pablodz/tesis_pregrado_pucp/Latex/trabajo-de-investigacion-1/images/chapter1/recepcion automatica por bombeo de peces mediante tuberia.pdf

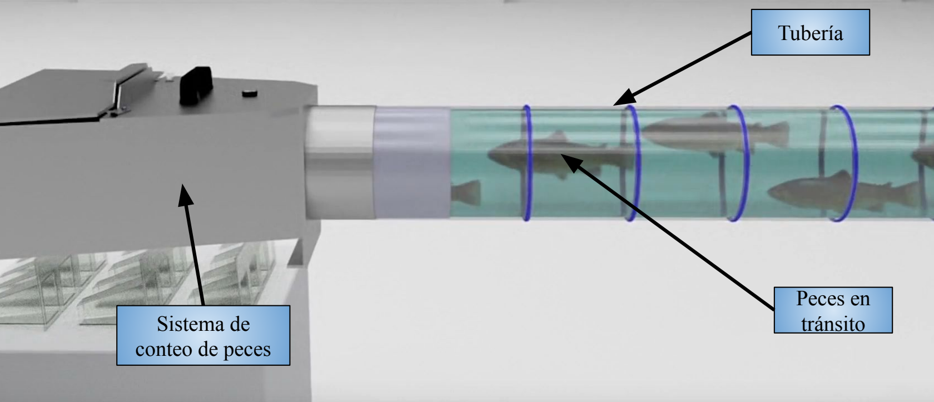
[picture p2: page 1]

Tubería

Peces en
Sistema de | tránsito
conteo de peces
