pablodz/tesis_pregrado_pucp/Latex/trabajo-de-investigacion-2/general/summary.tex

%----------------------------------------------------------------------------------------
%	Resumen
%----------------------------------------------------------------------------------------

\newpage
\clearpage{\pagestyle{empty}\cleardoublepage}
%\doublespacing
\newpage

\pagestyle{empty}
\pagenumbering{roman}
\newpage
\chapter*{\centering \large Resumen} 
\addcontentsline{toc}{chapter}{Resumen} % si queremos que aparezca en el índice
\markboth{Resumen}{Resumen} % encabezado

En el presente trabajo se desarrolla el diseño integral que comprende el diseño de ingeniería basándose en el diseño conceptual realizado en un trabajo previo. Consecuentemente, este trabajo detalla, calcula y evalúa aspectos técnicos del sistema en su conjunto que realiza una clasificación y conteo de truchas en la Laguna de Paucarcocha. La presente propuesta brinda una opción: un sistema semiautomatizado que tiene un precio inferior a las máquinas actualmente comerciables que se adapta a los requerimientos específicos dentro del mercado peruano y simplifica el proceso de clasificación con el fin de disminuir la alta mortandad presente en trabajos manuales. Las simulaciones demuestran un funcionamiento adecuado sistema de detección y conteo de truchas basado en algoritmos de detección de objetos de la arquitectura de redes neuronales YOLO aplicadas a imágenes adquiridas por una cámara estéreo. Finalmente, se concluye que se elaboró un sistema para la clasificación y conteo que sirve para las bases de un prototipo con un costo aproximado de \$4900.

%Considera los siguientes puntos:
%\begin{enumerate}
%	\item Desarrolle un único párrafo (200 a 300 palabras)
%	\item Escriba en tiempo verbal presente
%	\item El resumen debe contener información sobre:
%	\begin{itemize}
%		\item	- La justificación de la investigación
%		\item	- Los objetivos o hipótesis
%		\item	- La teoría o supuestos teóricos o metodológicos en la que se sustenta
%		\item	- El método o procedimiento realizado (de ser necesario)
%		\item	- Los resultados (de ser necesario)
%		\item	- La conclusión principal
%	\end{itemize}
%\end{enumerate}
