pablodz/tesis_pregrado_pucp/Latex/trabajo-de-investigacion-2/general/config.tex

%----------------------------------------------------------------------------------------
%	AUTOR DE LA CONFIGURACIÓN ACTUAL
%----------------------------------------------------------------------------------------

% Pablo Díaz Vergara
% Contáctamen en: pablo.diazv@pucp.edu.pe
% Revisa las últimas actualizaciones en:
% https://bit.ly/2EV6luX
% Versión Cofiguraciones: v2.2
% Fecha: 2020-12-04
% Github: https://github.com/ZurMaD/plantilla_tesis_pucp/

% AVISO: No modificar por su cuenta, enviar un correo para arreglar errores!

%----------------------------------------------------------------------------------------
%	NOMBRE DEL ARCHIVO
%----------------------------------------------------------------------------------------

% Eliminado por bugs en la visualización

%----------------------------------------------------------------------------------------
%	CONFIGURACION DOCUMENTO GENERAL
%----------------------------------------------------------------------------------------

\documentclass[12pt,a4paper,oneside]{thesis} % Formato tesis, 12 tamaño de letra
\setcounter{tocdepth}{4} % Número de indices a indexar en tabla de contenido 2:section 3:subsection 4:subsubsection
\setcounter{secnumdepth}{4} % Número de indices a indexar en tabla de contenido 2:section 3:subsection 4:subsubsection
\usepackage[english]{babel} % Asignar idioma por defecto spanish
%\selectlanguage{spanish} % Idioma por defecto x2
\usepackage[T1]{fontenc} % Aceptar caracteres con tíldes en el pdf generado
\usepackage[UTF8]{ctex}
\usepackage[utf8]{inputenc} % Aceptar caracteres con tíldes en Latex
\usepackage{amsmath} % Para mostrar de forma adecuada las ecuaciones
\usepackage{graphicx} % Para incluir imágenes 
\usepackage{array} % Para incluir imagenes en tablas https://bit.ly/2KXhIlu
\usepackage{float} % Para posicionar imágenes y tablas
\usepackage{multirow} % Fácil manejo de filas
\usepackage{longtable} % Para tablas que abarcan más de dos páginas
\usepackage[table,xcdraw]{xcolor} % Para tablas generadas en https://www.tablesgenerator.com/
% Tamaños de letra dentro de tablas https://texblog.org/2012/08/29/changing-the-font-size-in-latex/
\usepackage{multicol} % Para poder partir en columnas 
\usepackage[refpages]{gloss} % Para enumerar páginas
\usepackage{anysize} % OBSOLETO, NECESITA SER CAMBIADO
\usepackage{bigstrut} % Para automatizar ingresado de datos en tabla
\usepackage{appendix} % Formato para títulos de los apéndices
\usepackage{lscape} % Modifica margenes y rota la página pero no el enumerado
\usepackage{pdflscape} % Cambiar orientación en el pdf
\usepackage{listings} % Sirve para que se compile el Latex
\usepackage{color} % Colores de fondo, texto y otros
\usepackage{setspace} % Espacio entre lineas
\usepackage{enumerate} % Estilo del contador de páginas
\usepackage{ragged2e} % Formato de parrafos, justiticar y demás
\usepackage{comment} % Hacer comentarios en latex
\usepackage{pslatex} % Tipo de fuente
\usepackage{apacite} % Citación en APA
%\usepackage{fixltx2e} % Corrige bugs de Latex 3 | No es necesario en builds >2015
\usepackage{caption} % Objetos flotantes en el documento
\usepackage[top=2.54cm,
bottom=2.54cm,
left=2.54cm,
right=2.54cm,
headheight=17pt, % as per the warning by fancyhdr
includehead,includefoot,
heightrounded, % to avoid spurious underfull messages
]{geometry} % Márgenes para contenido y líneas de pie y cabecera de página
\usepackage{fancyhdr} % Cabeza y pie de página 
\usepackage{blindtext}
\usepackage{pdfpages} % Cargar imagenes en pdf
\usepackage{datetime} % Fecha

\usepackage{footnote} % Tablas largas y foot note para tablas https://texblog.org/2012/02/03/using-footnote-in-a-table/
\usepackage{enumitem} % Enumerar letras
\usepackage[bottom]{footmisc} % Forzar notas de página pegadas hacia abajo https://bit.ly/3fyOA2f
\usepackage{scrextend} % Cambiar formato nota de página
\deffootnote[.5in]{.5in}{.195in}{\makebox[.5in][r]{\thefootnotemark.\hspace{.2in}}}  % Cambiar formato nota de página
% ERROR DE "TITLE ALREADY DEFINED" Pueden omitirlo, no afecta en nada, pueden comentarlo incluso en el archivo.sty

\usepackage[paper=portrait,pagesize]{typearea} %PORTRAID-LANDSCAPE 

\usepackage{url} % Evitar enlaces en bibliografía largos & enlazar enlaces de bibliografía
\usepackage{breakurl} % Broken links
\usepackage[hyperfootnotes=false]{hyperref} % Evitar enlaces en bibliografía largos & enlazar enlaces de bibliografía ADEMAS, false porque así lo recomienda la libreria footmisc
\usepackage{natbib}
\usepackage{etoolbox}

\usepackage{mathptmx} % Times News Roman
\usepackage{titlesec} % Cambiar chapter style
\usepackage{indentfirst} % Agregar indentado de 1cm al inicio de cada párrafo de cada sección

%\usepackage{svg} % Soporte imagenes svg
% SVG necesita agregar --shel por eso no lo usaremos

%----------------------------------------------------------------------------------------
%	CONFIGURACION ESPACIADO, TAMAÑO DE LETRA Y RELACIONADOS A FIGURAS, TABLAS
%----------------------------------------------------------------------------------------
% Documentación \captionsetup https://bit.ly/31RjwG3 

% FIGURAS
\captionsetup[figure]{font={footnotesize,singlespacing}} % https://bit.ly/2QOHo6U
\captionsetup[figure]{labelfont={bf}} % Negrita a Tabla X.X
\captionsetup[figure]{labelsep={endash}} % Punto y espacio luego de Figura X.X. 
\captionsetup[figure]{width={.75\textwidth}} % Sangría para título de Figura
\captionsetup[figure]{justification=centerlast} % Justificado, última linea centrado
\captionsetup[figure]{aboveskip=7pt} % https://bit.ly/3jIe7HF Foro latex
\captionsetup[figure]{belowskip=7pt} 
\captionsetup[figure]{skip=0pt} % Posición figuras
\captionsetup[figure]{position=below} % Posición figuras
\captionsetup[figure]{name=Figura} % Nombre figuras

% TABLAS
\captionsetup[table]{font={footnotesize,singlespacing}} % scriptsize,footnotesize,small,normalsize,larga,Large %stretch=0.8
\captionsetup[table]{labelfont={bf}} % normalfont,up,it,sl,sc,md,bf,rm,sf,tt
\captionsetup[table]{labelsep={endash}} % none,colon,period,space,quad,newline,endash 
\captionsetup[table]{width={.75\textwidth}} % Sangría para título de tabla
\captionsetup[table]{justification=centerlast} % Justificado, última linea centrado
\captionsetup[table]{aboveskip=7pt} % Espaciado arriba del título
\captionsetup[table]{belowskip=7pt} % Espaciado abajo del título
\captionsetup[table]{skip=0pt} % Posición tablas
\captionsetup[table]{position=above} % Posición tablas
\captionsetup[table]{name=Tabla} % Nombre figuras

%----------------------------------------------------------------------------------------
%	CONFIGURACION SECCIONES DE CÓDIGO
%----------------------------------------------------------------------------------------

% Eliminado, contenia bugs, la siguiente versión se implementa

%----------------------------------------------------------------------------------------
%	CONFIGURACION FORMATO SECCIONES
%----------------------------------------------------------------------------------------

%%%%%%%%%%%%%%%%%%%%%%%%%%%%%%%%%%%%%%%%%%%%%%%%%%%%%%
% PÁGINA DE CAPÍTULOS ES AUTOMÁTICO TIPO PLAIN       %
%%%%%%%%%%%%%%%%%%%%%%%%%%%%%%%%%%%%%%%%%%%%%%%%%%%%%%
\fancypagestyle{plain}{
	\fancyhead{}% clear all header 
	\fancyfoot{}% clear all footer
	\fancyhf{}% clear all header and footer fields	
	\fancyhead[L,C,R]{}
	\fancyfoot[L,C,R]{}
	\fancyfoot[C]{Página \thepage}
	\renewcommand{\headrulewidth}{0.4pt}
	\renewcommand{\footrulewidth}{0.4pt}
	\newgeometry{
		top=2.54cm,
		bottom=2.54cm,
		left=2.54cm,
		right=2.54cm,
		headheight=17pt, % as per the warning by fancyhdr
		includehead,includefoot,
		heightrounded % to avoid spurious underfull messages
	}
}
%%%%%%%%%%%%%%%%%%%%%%%%%%%%%%%%%%%%%%%%%%%%%%%%%%%%%%
% PÁGINA VERTICAL                                    %
%%%%%%%%%%%%%%%%%%%%%%%%%%%%%%%%%%%%%%%%%%%%%%%%%%%%%%
\fancypagestyle{myportland}{
	\fancyhead{}% clear all header 
	\fancyfoot{}% clear all footer
	\fancyhf{}% clear all header and footer fields	
	\fancyhead[L,C,R]{}
	\fancyfoot[L,C,R]{}
	\fancyfoot[C]{Página \thepage}
	\renewcommand{\headrulewidth}{0.4pt}
	\renewcommand{\footrulewidth}{0.4pt}
	\newgeometry{
		top=2.54cm,
		bottom=2.54cm,
		left=2.54cm,
		right=2.54cm,
		headheight=17pt, % as per the warning by fancyhdr
		includehead,includefoot,
		heightrounded % to avoid spurious underfull messages
	}
}
%%%%%%%%%%%%%%%%%%%%%%%%%%%%%%%%%%%%%%%%%%%%%%%%%%%%%%
% PÁGINA HORIZONTAL                                  %
%%%%%%%%%%%%%%%%%%%%%%%%%%%%%%%%%%%%%%%%%%%%%%%%%%%%%%
% https://tex.stackexchange.com/questions/337/how-to-change-certain-pages-into-landscape-portrait-mode
\fancypagestyle{mylandscape}{
	\fancyhead{}% clear all header 
	\fancyfoot{}% clear all footer
	\fancyhf{}% clear all header and footer fields	
	\fancyhead[LO,RE]{}
	\fancyfoot[LO,RE]{}
	\fancyfoot{% Footer
		\makebox[\textwidth][r]{% Right
			\rlap{\hspace{0.75cm}% Push out of margin by \footskip
				\smash{% Remove vertical height
					\raisebox{4.87in}{% Raise vertically
						\rotatebox{90}{Página \thepage}}}}}}% Rotate counter-clockwise
	\renewcommand{\headrulewidth}{0pt}% No header rule
	\renewcommand{\footrulewidth}{0pt}% No footer rule
	\newgeometry{
		top=3.54cm, % Now top is → right
		bottom=2.54cm, % Now botton is ← left
		left=2.40cm, % Now left is ↑ top
		right=2cm, % Now right is ↓ bottom
	}
}

%----------------------------------------------------------------------------------------
%	UTILIDADES
%----------------------------------------------------------------------------------------

\newcommand*\rot{\rotatebox{90}} % Poder rotar 90° texto, imagenes, lo que sea
\graphicspath{{images/}} % Directorio que contiene imagenes

%----------------------------------------------------------------------------------------
%	CONFIGURACION NOMBRE DE TÍTULOS, CAPÍTULOS, TABLAS, ÍNDICES
%----------------------------------------------------------------------------------------

%%%%%%%%%%%%%%%%%%%%%%%%%%%%%%%%%%%%%%%%%%%%%%%%%%%%%%
% CAMBIO DE FORMATO DE CAPÍTULOS                     %
%%%%%%%%%%%%%%%%%%%%%%%%%%%%%%%%%%%%%%%%%%%%%%%%%%%%%%

% CHAPTER X
\titleformat{\chapter}
{\large\bfseries\filcenter}{\thechapter}{1em}{}
% SECTION X.X
\titleformat{\section}
{\normalfont\bfseries\filright}{\thesection}{1em}{}

% SUBSECTION X.X.X
\titleformat{\subsection}
{\normalfont\bfseries\filright}{\thesubsection}{1em}{}

% SUBSUBSECTION X.X.X.X
\titleformat{\subsubsection}
{\normalfont\bfseries\filright}{\thesubsubsection}{1em}{}

% Dentro del siguiente código no usar comentarios
% ENUMERACIÓN arabic Arabic Roman roman
\addto\captionsenglish{
	\renewcommand{\contentsname}{Índice}
	\renewcommand{\listfigurename}{Índice de figuras}
	\renewcommand{\listtablename}{Índice de tablas}
	\renewcommand{\baselinestretch}{2}
	\renewcommand{\appendixname}{Anexos}
	\renewcommand{\appendixtocname}{Anexos}
	\renewcommand{\appendixpagename}{Anexos}
	\renewcommand{\chaptername}{Capítulo}
	\renewcommand{\thetable}{Tabla}	
	\renewcommand{\thefigure}{Figura}
	\renewcommand{\thechapter}{Capítulo \arabic{chapter}}
	\renewcommand{\thesection}{\arabic{chapter}.\arabic{section}}
	\renewcommand{\thetable}{\arabic{chapter}.\arabic{table}}
	\renewcommand{\thefigure}{\arabic{chapter}.\arabic{figure}}
	\renewcommand{\theequation}{\arabic{chapter}.\arabic{equation}}
}

\renewcommand{\bibsection}{} % Eliminar "References" como título de lista de bibliografía

%%%%%%%%%%%%%%%%%%%%%%%%%%%%%%%%%%%%%%%%%%%%%%%%%%%%%%
% MODO 1: ENUMERACIÓN POR CAPÍTULOS 1.1,1.2,2.1,...  %
%%%%%%%%%%%%%%%%%%%%%%%%%%%%%%%%%%%%%%%%%%%%%%%%%%%%%%
%\renewcommand{\thetable}{\arabic{chapter}.\arabic{table}}
%\renewcommand{\thefigure}{\arabic{chapter}.\arabic{figure}}
%\renewcommand{\theequation}{\arabic{chapter}.\arabic{equation}}
%%%%%%%%%%%%%%%%%%%%%%%%%%%%%%%%%%%%%%%%%%%%%%%%%%%%%%
% MODO 2: ENUMERACIÓN ARÁBICA SECUENCIAL 1,2,3,4,... %
%%%%%%%%%%%%%%%%%%%%%%%%%%%%%%%%%%%%%%%%%%%%%%%%%%%%%%
%\renewcommand{\thetable}{\arabic{1}}
%\renewcommand{\thefigure}{\arabic{1}}
%\renewcommand{\theequation}{\arabic{1}}

%----------------------------------------------------------------------------------------
%	CONSTANTES GLOBALES
%----------------------------------------------------------------------------------------

\newcommand{\myarraystrech}{0.75}

\newcommand{\mymaxsizeofcontenttable}{3 cm}
\newcommand{\mysizeimageinsidetable}{1.5 cm}

\newcommand{\mysecondmaxsizeofcontenttable}{5 cm}
\newcommand{\mysecondmaxsizeimageinsidetable}{4 cm}

\newcommand{\mythirdmaxsizeofcontenttable}{2.6 cm}
\newcommand{\mythirdmaxsizeimageinsidetable}{2.4 cm}

\newcommand{\myforthmaxsizeofcontenttable}{4 cm}

\newenvironment{myflushcenter}{%
	\vspace{-1.5em}
	\begin{center}
	}{%
	\end{center}
}

\newenvironment{myflushcenterinsidetable}{%
	\setstretch{0.75}
	\setlength\topsep{0pt}
	\setlength\parskip{0pt}
	\begin{center}
	}{%
	\end{center}
}

\newenvironment{myflushleftinsidetable}{%
	\setstretch{0.75}
	\setlength\topsep{0pt}
	\setlength\parskip{0pt}
	\begin{flushleft}
	}{%
	\end{flushleft}
}

\newenvironment{myflushcenteraftertable}{%
	\vspace{-0.5 em}
	\begin{center}
	}{%
	\end{center}
}

% Para datos debajo de imagenes en páginas verticales
\newenvironment{myflushleftportland}{%
	\vspace{-1.5em}
	\begin{flushleft} 
	\footnotesize
	}{%
	\end{flushleft}
}

% Para datos debajo de tablas en páginas verticales
\newenvironment{myflushleftportland2}{%
	\vspace{-2.5em}
	\begin{flushleft} 
	\footnotesize
	}{%
	\end{flushleft}
}

% Para datos debajo de tablas e imagenes en páginas verticales
\newenvironment{myflushleftlandscape}{%
	\vspace{-3em}
	\begin{flushleft} 
	\footnotesize
	}{%
	\end{flushleft}
}

% Para evitar espacios luego de nombre de imagen
\newenvironment{myfigure}{%
	\vspace{-0.10em}
	\begin{figure}
	}{%
	\end{figure}
	\vspace{-1.5em}
}

% Para evitar espacios luego de la tabla
\newenvironment{mytable}{%
	\vspace{-1.0em}
	\begin{table}
	}{%
	\end{table}
	\vspace{-1.5em}
}

% Para evitar espacios en ecuaciones
\newenvironment{myequation}{%
	\vspace{-2.5em}
	\begin{equation}
	}{%
	\end{equation}
	\vspace{-2.0em}
}

%----------------------------------------------------------------------------------------
%	CONFIGURACION BIBLIOGRAFIA
%----------------------------------------------------------------------------------------

\bibliographystyle{apacite}
\renewcommand{\BOthers}[1]{et al.\hbox{}}%       et al
\renewcommand{\BOthersPeriod}[1]{et al.\hbox{}}%  et al.
% CONTINUA EN BIBLIOGRAPHY.TEX

%----------------------------------------------------------------------------------------
%	CONFIGURACION DE MARGENES EN TABLA DE CONTENIDOS, COMENTAR SI QUIERES QUE SALGA CON INDENTADOS
%----------------------------------------------------------------------------------------

% Será actualizado en la siguiente versión...

%----------------------------------------------------------------------------------------
%	CONFIGURACION NOTAS DE PAGINA
%----------------------------------------------------------------------------------------

\setlength{\footskip}{25pt} % Elimina espacios luego de notas de pagina
