pablodz/tesis_pregrado_pucp/Latex/trabajo-de-investigacion-1/general/conclusions.tex

%----------------------------------------------------------------------------------------
%	Agradecimientos
%----------------------------------------------------------------------------------------

\pagestyle{myportland}
\doublespacing
%\pagenumbering{arabic}
\chapter*{\centering \large Conclusiones}
\addcontentsline{toc}{chapter}{Conclusiones}
\markboth{Conclusiones}{Conclusiones}
\thispagestyle{myportland}

Se detectaron procesos críticos en la crianza de truchas y se seleccionó el proceso manual que disminuía la producción final generando pérdidas económicas: clasificación y conteo de truchas en la etapa de engorde (15 a 20 centímetros).

Se elaboró la lista de requerimientos según una entrevista con personas dedicadas al cultivo de truchas. Se propuso tres conceptos de solución y se escogió uno de estos bajo un análisis técnico-económico. El concepto de solución óptimo cumple con todos los puntos de la lista de requerimientos. Además, se realizó el diagrama de operaciones necesario para mostrar el funcionamiento de la máquina.

Para el análisis de estabilidad y flotabilidad sobre el agua del concepto de solución óptimo será necesario realizar cálculos y mediciones.

Una estimación simple sin detalle del concepto de solución óptimo muestra un costo menor comparado con el costo de una máquina que se comercializa internacional-mente. Además, el costo de operación disminuye debido a que se reduce el número de operarios de cuatro a solo uno.

El trabajo presentado permite la extrapolación de dimensiones de las tuberías para poder emplear diferentes tallas de truchas. Es decir, una máquina de clasificación y conteo fuera del rango propuesto de 10 a 20 cm.
