pablodz/tesis_pregrado_pucp/Latex/trabajo-de-investigacion-1/images/chapter3/concepto virtual del concepto de solucion 2.pdf

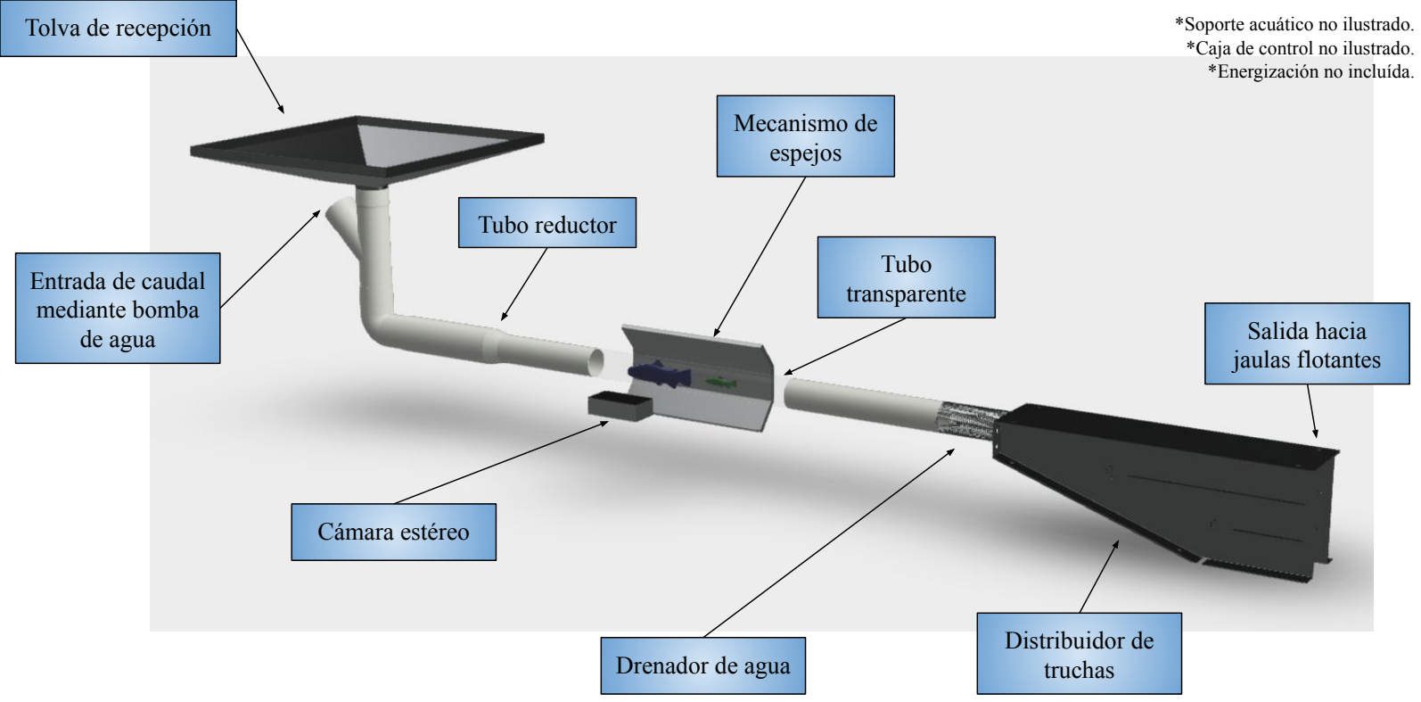
[picture p191: page 1]

Tolva de recepción

Entrada de caudal
mediante bomba
de agua

Cámara estéreo

Drenador de agua

Distribuidor de
truchas

Salida hacia
jaulas flotantes

Tubo reductor

Tubo
transparente

Mecanismo de
espejos

*Soporte acuático no ilustrado. *Caja de control no ilustrado. *Energización no incluída.
