pablodz/tesis_pregrado_pucp/Latex/trabajo-de-investigacion-1/images/chapter1/maquina seleccionadora de truchas agv.pdf

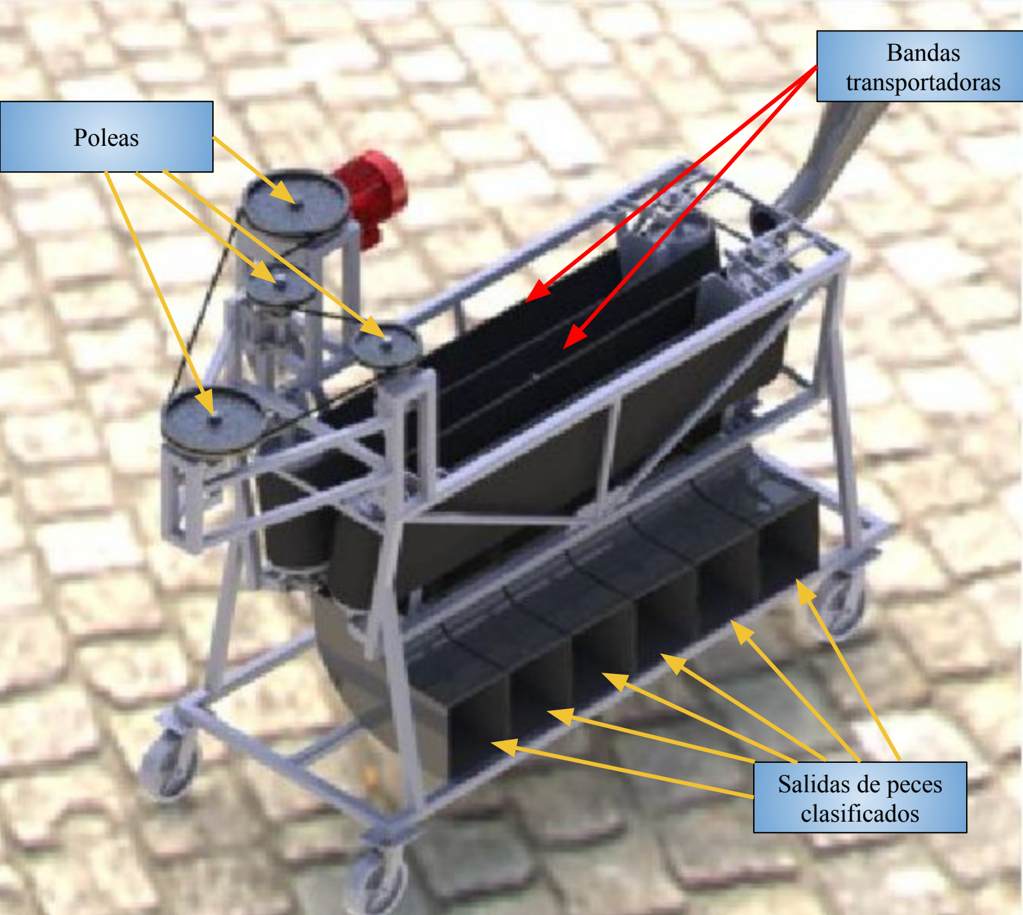
[picture p192: page 1]

Bandas
transportadoras

Salidas de peces
clasificados

Poleas
