pablodz/tesis_pregrado_pucp/Latex/trabajo-de-investigacion-1/images/chapter1/contador pescavision 100 300 10x4.pdf

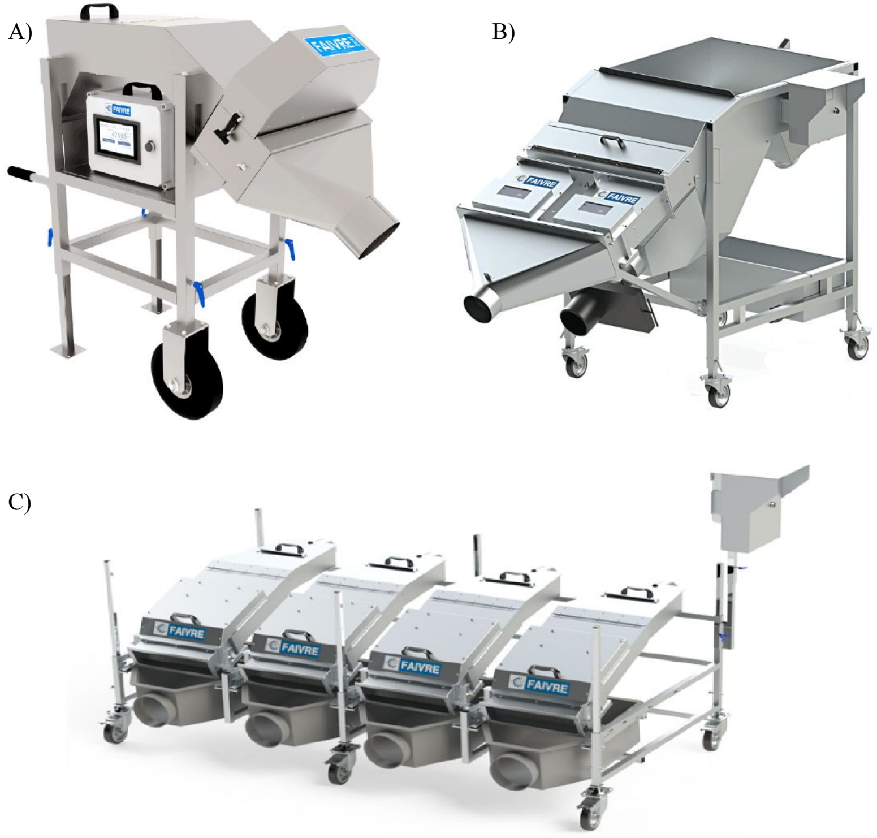
[picture p193: page 1]

A) B)

C)
