pablodz/tesis_pregrado_pucp/Latex/trabajo-de-investigacion-1/images/chapter1/clasificacion conteo curado y calculo de biomasa en la laguna de canrash.pdf

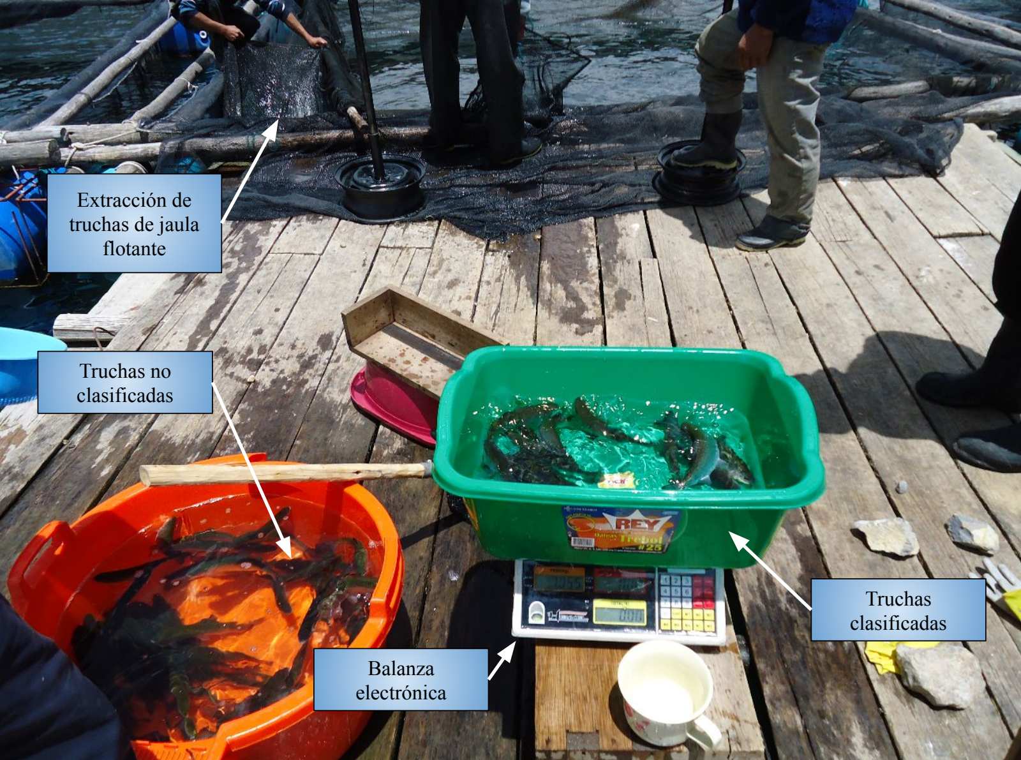
[picture p194: page 1]

Extracción de
truchas de jaula
flotante

Truchas no
clasificadas

Balanza
electrónica

Truchas
clasificadas
