pablodz/tesis_pregrado_pucp/Latex/trabajo-de-investigacion-1/images/chapter1/extraccion de caracteristicas mediante vision por computadora.pdf

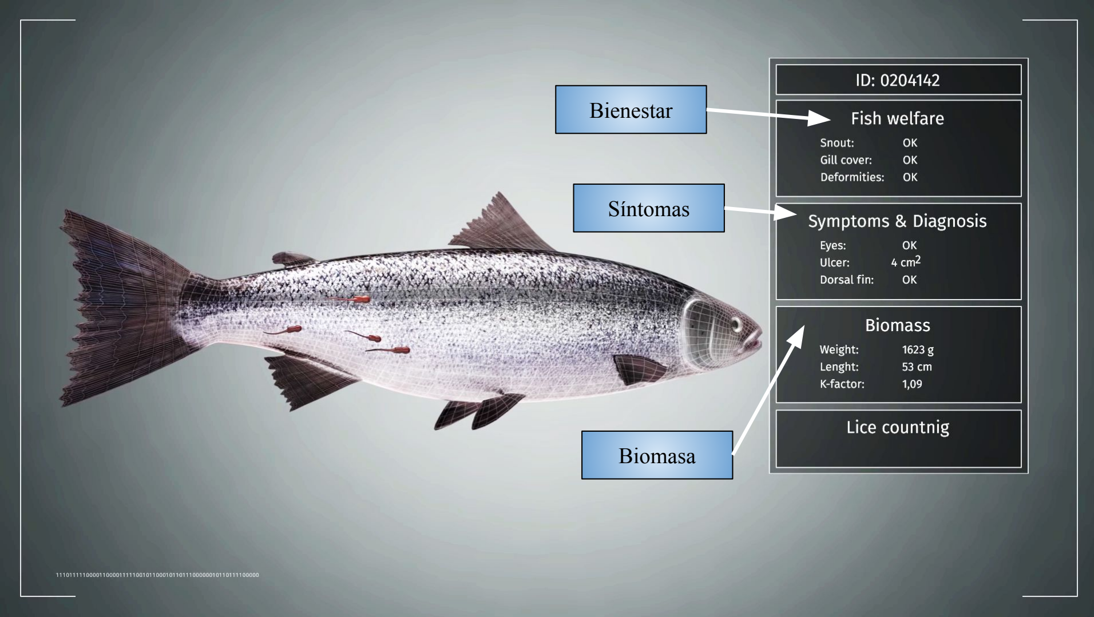
[picture p195: page 1]

Bienestar

Síntomas

Biomasa
