pablodz/tesis_pregrado_pucp/Latex/trabajo-de-investigacion-1/images/chapter1/planos comunes de posicionamiento para camaras de inspeccion.pdf

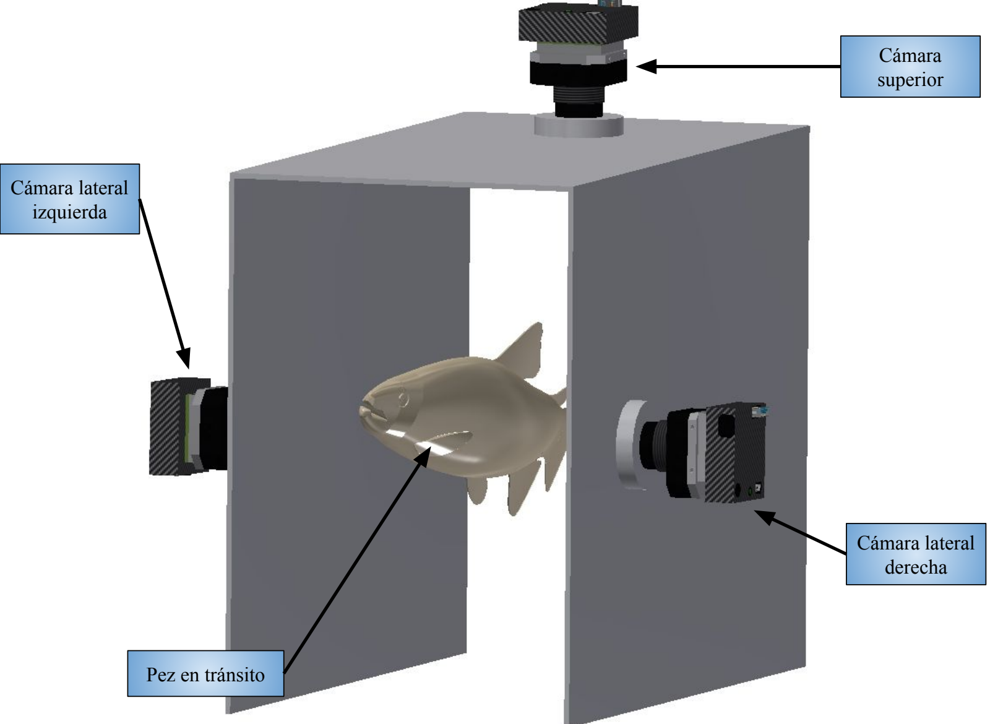
[picture p196: page 1]

Cámara lateral
izquierda

Pez en tránsito

Cámara
superior

Cámara lateral
derecha
