pablodz/tesis_pregrado_pucp/Latex/trabajo-de-investigacion-1/images/chapter1/usando relacion entre a y b para calcular longitud del pez.pdf

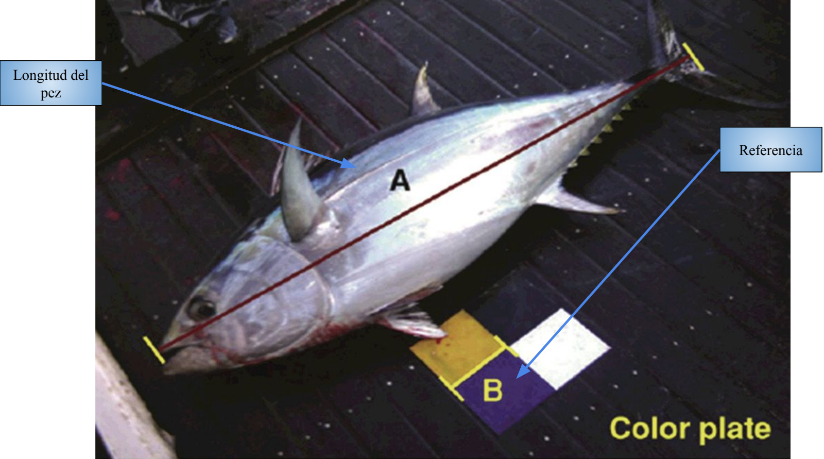
[picture p197: page 1]

Referencia

Longitud del
pez
