pablodz/tesis_pregrado_pucp/Latex/trabajo-de-investigacion-1/images/chapter1/extraccion trucha toneladas anuales.png

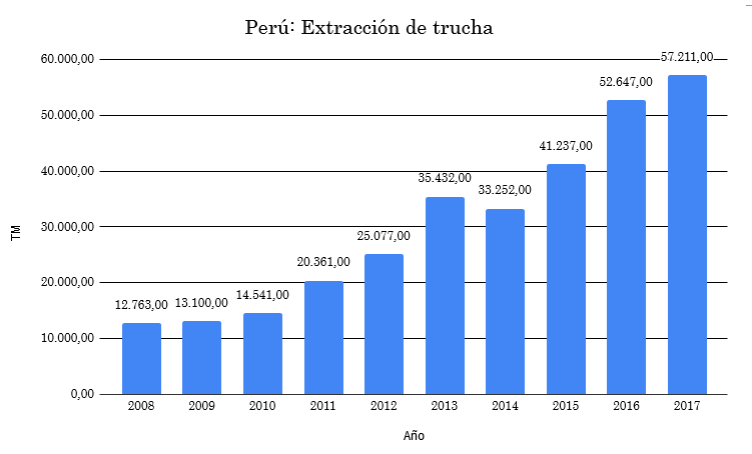
Latex/trabajo-de-investigacion-1/images/chapter1/extraccion trucha toneladas anuales.png
