pablodz/tesis_pregrado_pucp/Latex/trabajo-de-investigacion-1/images/chapter1/medicion de peces dentro de estanques con camaras ortogonales.png

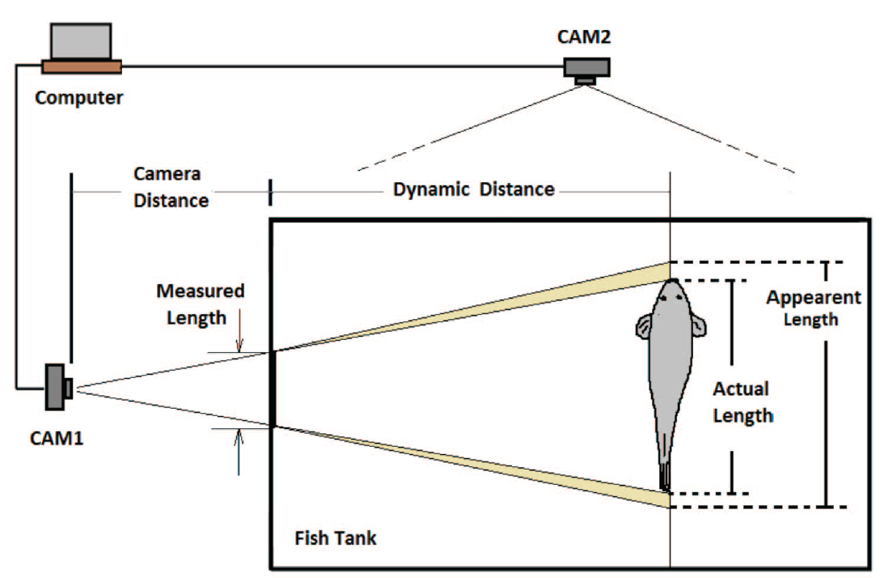
Latex/trabajo-de-investigacion-1/images/chapter1/medicion de peces dentro de estanques con camaras ortogonales.png
