pablodz/tesis_pregrado_pucp/Latex/trabajo-de-investigacion-1/images/chapter1/pez identificado por una red neuronal.png

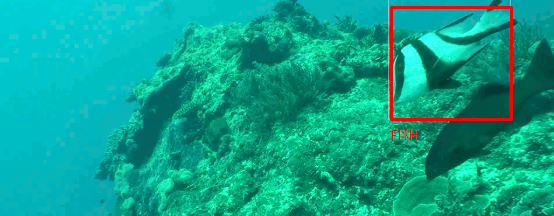
Latex/trabajo-de-investigacion-1/images/chapter1/pez identificado por una red neuronal.png
