pablodz/tesis_pregrado_pucp/Latex/trabajo-de-investigacion-1/images/chapter3/matriz/fuente de alimentacion.png

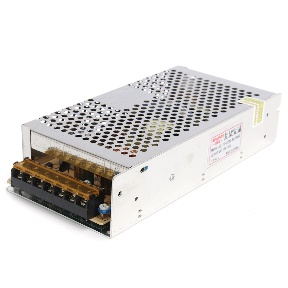
Latex/trabajo-de-investigacion-1/images/chapter3/matriz/fuente de alimentacion.png
