pablodz/tesis_pregrado_pucp/Latex/trabajo-de-investigacion-1/images/chapter3/matriz/tarjeta electronica para control de actuadores lineales.png

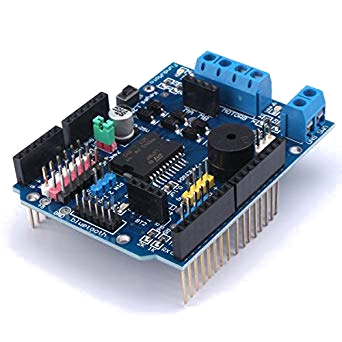
Latex/trabajo-de-investigacion-1/images/chapter3/matriz/tarjeta electronica para control de actuadores lineales.png
