pablodz/tesis_pregrado_pucp/Latex/trabajo-de-investigacion-1/images/chapter3/matriz/variador de voltaje.png

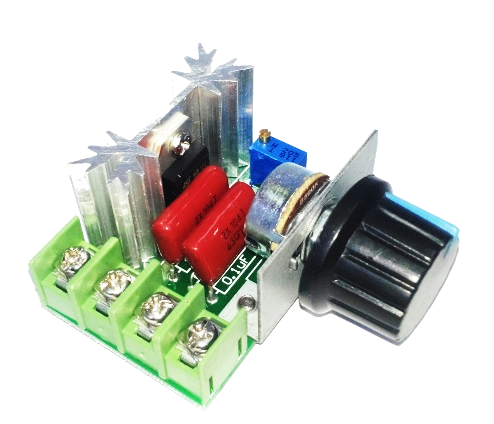
Latex/trabajo-de-investigacion-1/images/chapter3/matriz/variador de voltaje.png
