pablodz/tesis_pregrado_pucp/Latex/trabajo-de-investigacion-1/images/introduction/produccion agricola mundial.png

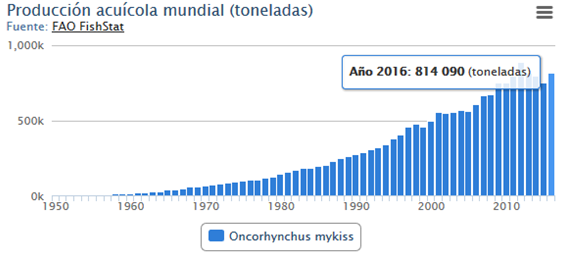
Latex/trabajo-de-investigacion-1/images/introduction/produccion agricola mundial.png
