pablodz/tesis_pregrado_pucp/Latex/trabajo-de-investigacion-2/images/chapter1/medicion de peces dentro de estanques con camaras estereo.png

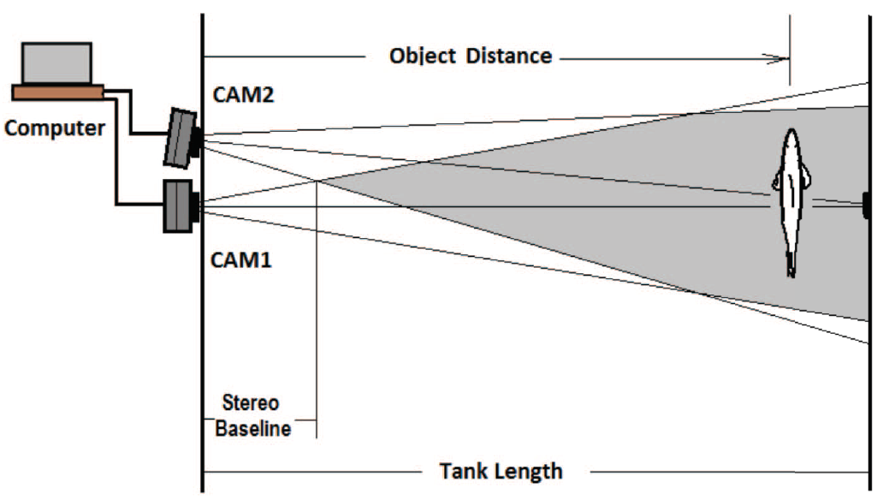
Latex/trabajo-de-investigacion-2/images/chapter1/medicion de peces dentro de estanques con camaras estereo.png
