pablodz/tesis_pregrado_pucp/Latex/trabajo-de-investigacion-2/images/chapter3/matriz/boton de emergencia.png

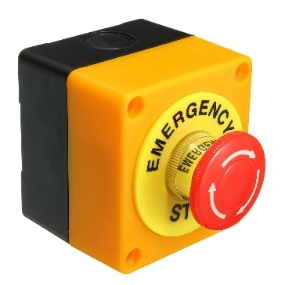
Latex/trabajo-de-investigacion-2/images/chapter3/matriz/boton de emergencia.png
