pablodz/tesis_pregrado_pucp/Latex/trabajo-de-investigacion-2/images/chapter5/aplicacion movil login.png

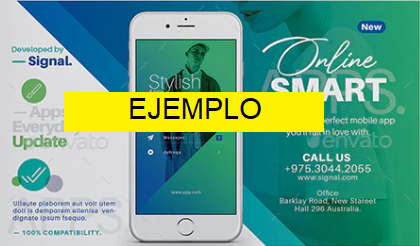
Latex/trabajo-de-investigacion-2/images/chapter5/aplicacion movil login.png
