pablodz/tesis_pregrado_pucp/Latex/trabajo-de-investigacion-2/images/chapter5/concepto optimo tuberias.png

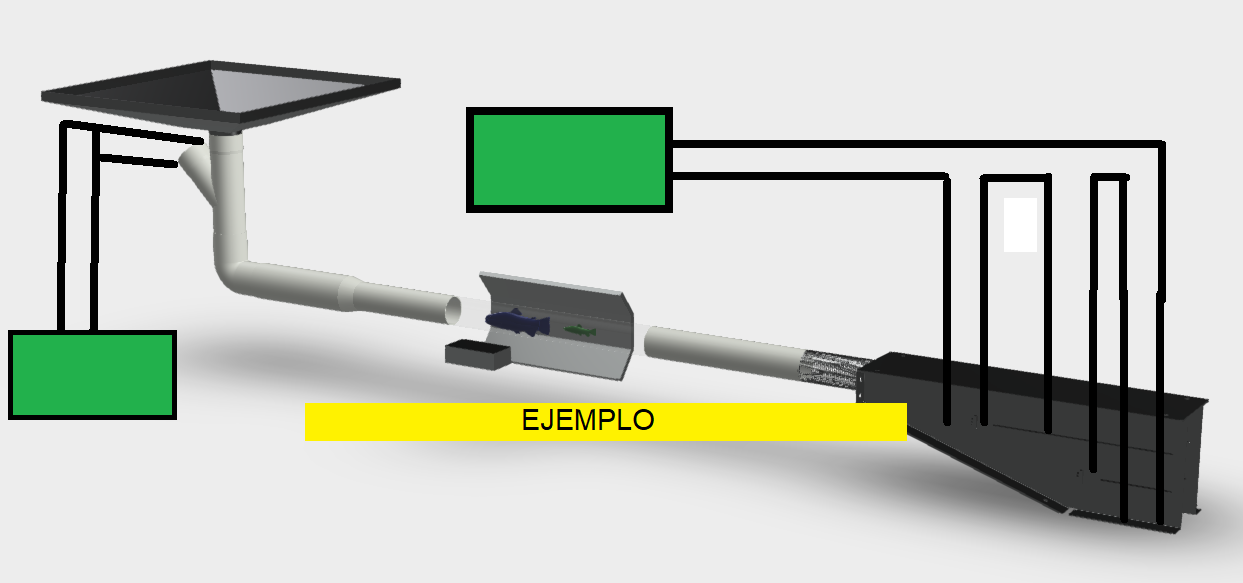
Latex/trabajo-de-investigacion-2/images/chapter5/concepto optimo tuberias.png
