pablodz/tesis_pregrado_pucp/Latex/trabajo-de-investigacion-2/images/chapter5/control electrovalvulas pid.png

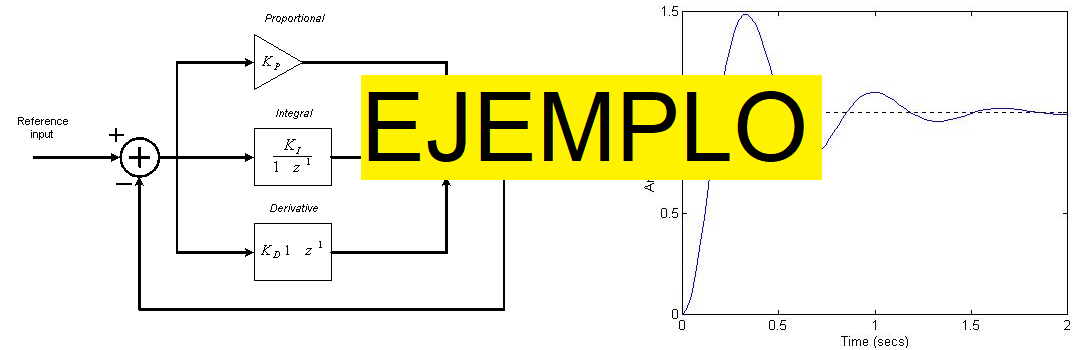
Latex/trabajo-de-investigacion-2/images/chapter5/control electrovalvulas pid.png
