pablodz/tesis_pregrado_pucp/Latex/trabajo-de-investigacion-2/images/chapter5/distancia entre espejos y camara ejemplo.png

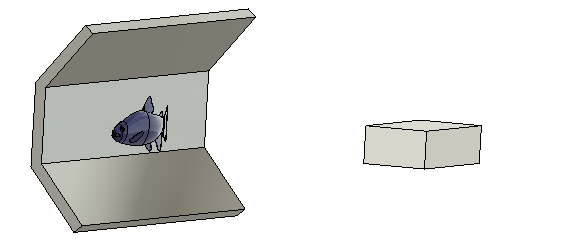
Latex/trabajo-de-investigacion-2/images/chapter5/distancia entre espejos y camara ejemplo.png
