pablodz/tesis_pregrado_pucp/Latex/trabajo-de-investigacion-2/images/chapter5/ejemplo de tabla.png

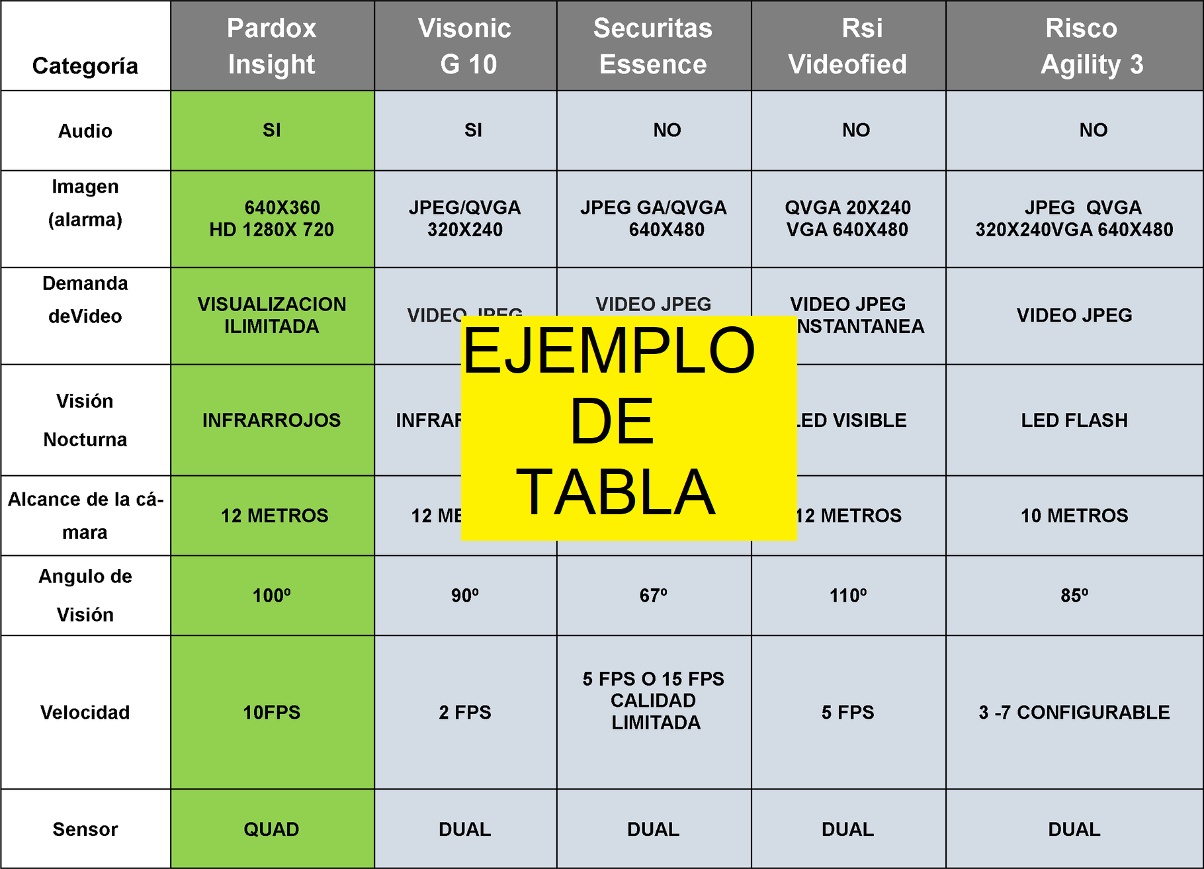
Latex/trabajo-de-investigacion-2/images/chapter5/ejemplo de tabla.png
