pablodz/tesis_pregrado_pucp/Latex/trabajo-de-investigacion-2/images/chapter5/frontend/frames (6).png

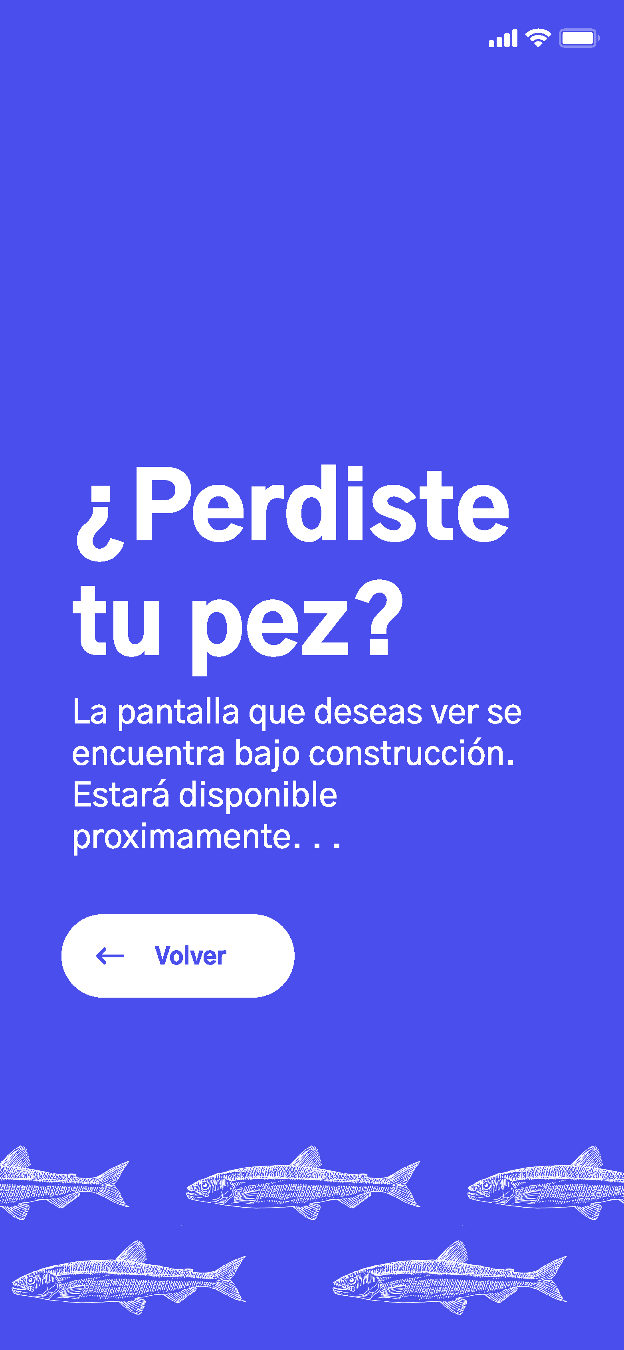
Latex/trabajo-de-investigacion-2/images/chapter5/frontend/frames (6).png
