pablodz/tesis_pregrado_pucp/Latex/trabajo-de-investigacion-2/images/chapter5/frontend/frames (9).png

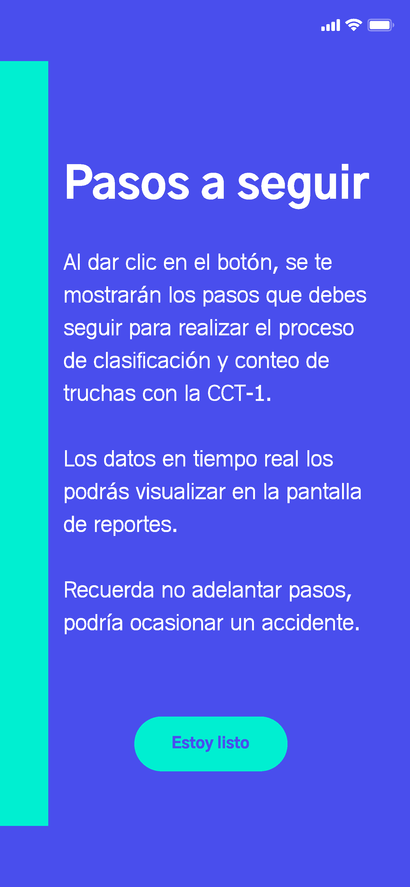
Latex/trabajo-de-investigacion-2/images/chapter5/frontend/frames (9).png
