pablodz/tesis_pregrado_pucp/Latex/trabajo-de-investigacion-2/images/chapter5/iluminacion 2 tiras led.png

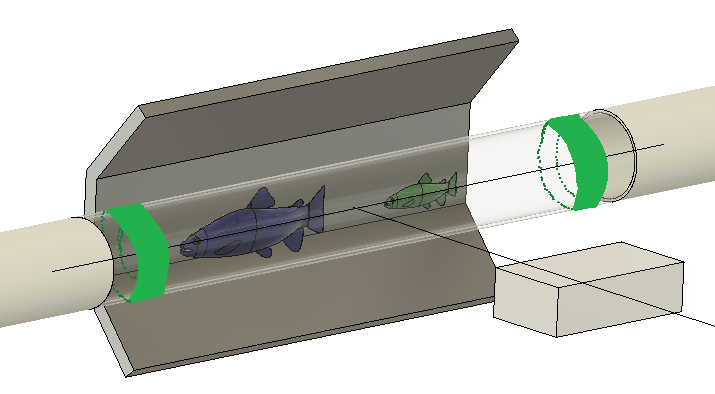
Latex/trabajo-de-investigacion-2/images/chapter5/iluminacion 2 tiras led.png
