pablodz/tesis_pregrado_pucp/Latex/trabajo-de-investigacion-2/images/chapter5/iluminacion 4 leds.png

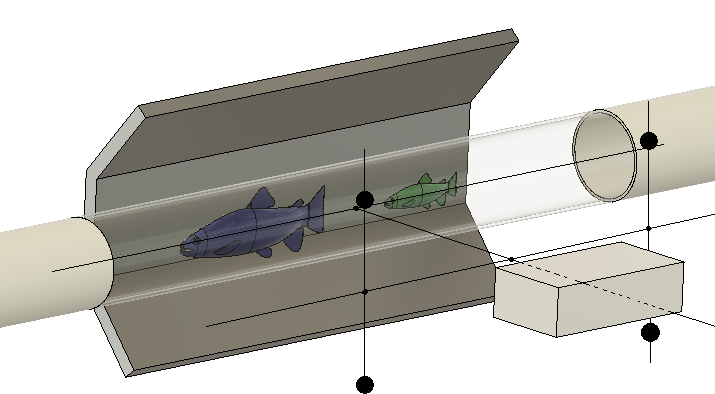
Latex/trabajo-de-investigacion-2/images/chapter5/iluminacion 4 leds.png
