pablodz/tesis_pregrado_pucp/Latex/trabajo-de-investigacion-2/images/chapter5/mecanismo de compuertas engranajes.png

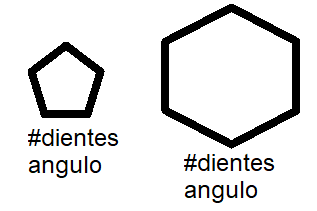
Latex/trabajo-de-investigacion-2/images/chapter5/mecanismo de compuertas engranajes.png
