pablodz/tesis_pregrado_pucp/Latex/trabajo-de-investigacion-2/images/chapter5/posicion sensor infrarrojo ejemplo.png

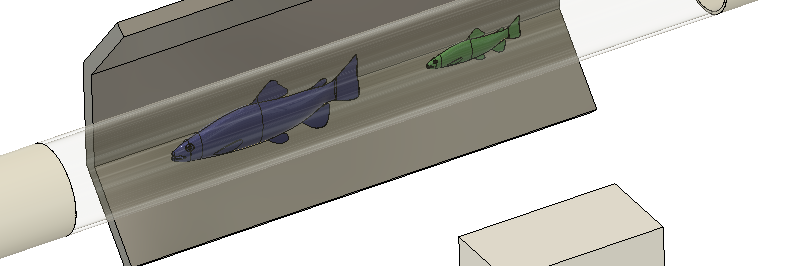
Latex/trabajo-de-investigacion-2/images/chapter5/posicion sensor infrarrojo ejemplo.png
