pablodz/tesis_pregrado_pucp/Latex/trabajo-de-investigacion-2/images/chapter5/potencia requerida por componente.png

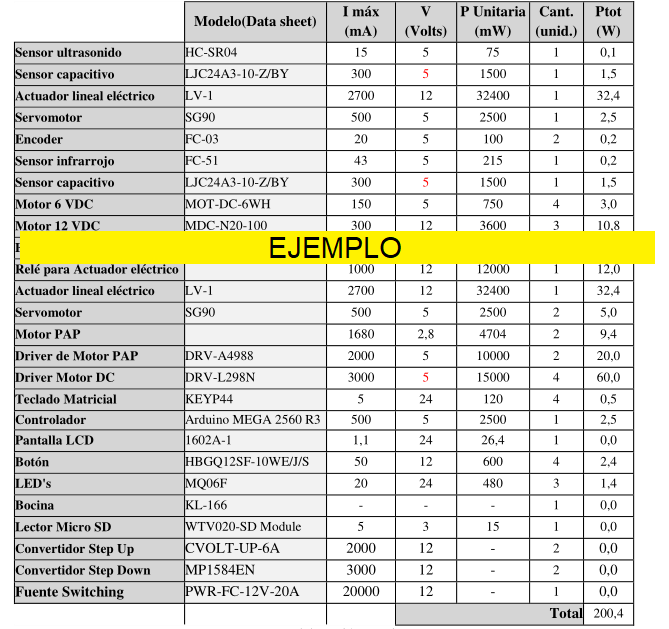
Latex/trabajo-de-investigacion-2/images/chapter5/potencia requerida por componente.png
