pablodz/tesis_pregrado_pucp/Latex/trabajo-de-investigacion-2/images/chapter5/renders/distribuidora 6.png

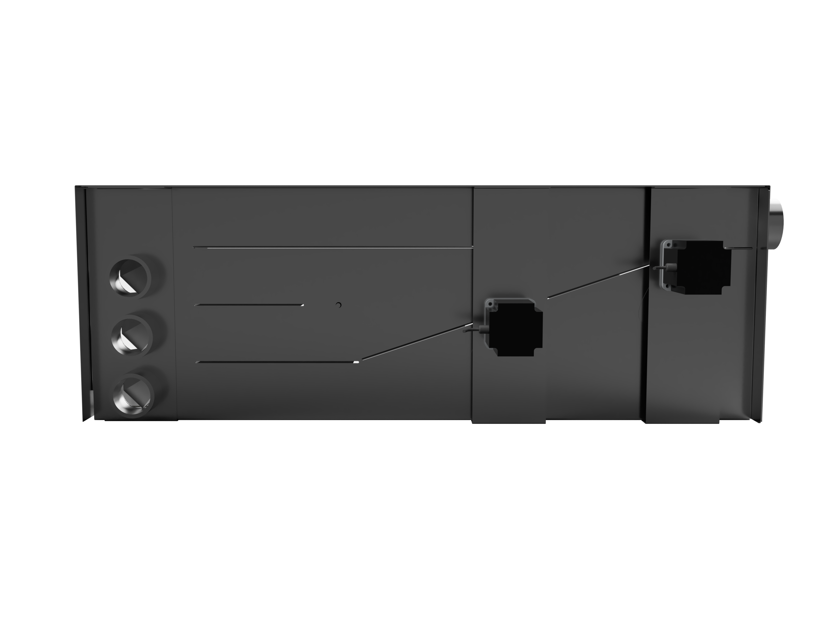
Latex/trabajo-de-investigacion-2/images/chapter5/renders/distribuidora 6.png
