pablodz/tesis_pregrado_pucp/Latex/trabajo-de-investigacion-2/images/chapter5/subsistema de flotacion.png

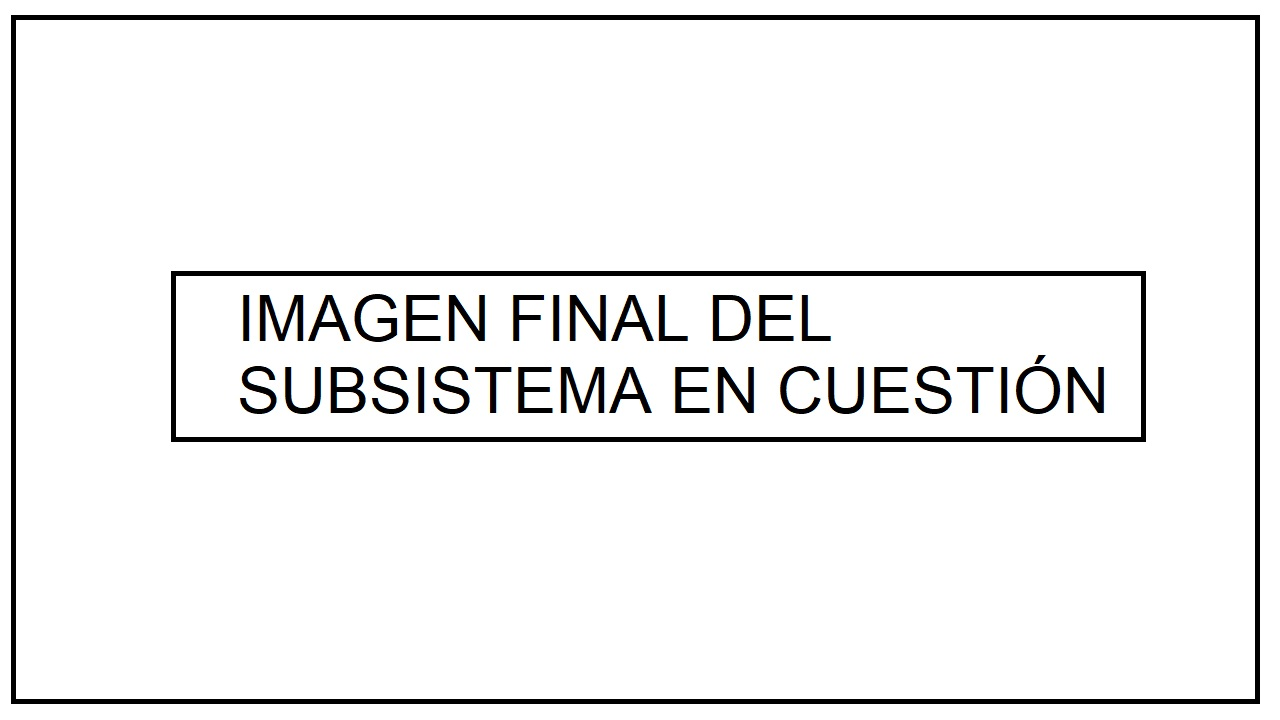
Latex/trabajo-de-investigacion-2/images/chapter5/subsistema de flotacion.png
