pablodz/tesis_pregrado_pucp/Latex/trabajo-de-investigacion-2/images/chapter5/tablas comparativas/bomba de agua sumergible 1.png

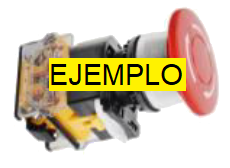
Latex/trabajo-de-investigacion-2/images/chapter5/tablas comparativas/bomba de agua sumergible 1.png
