pablodz/tesis_pregrado_pucp/Latex/trabajo-de-investigacion-2/images/chapter5/tablas comparativas/camara simple 3.png

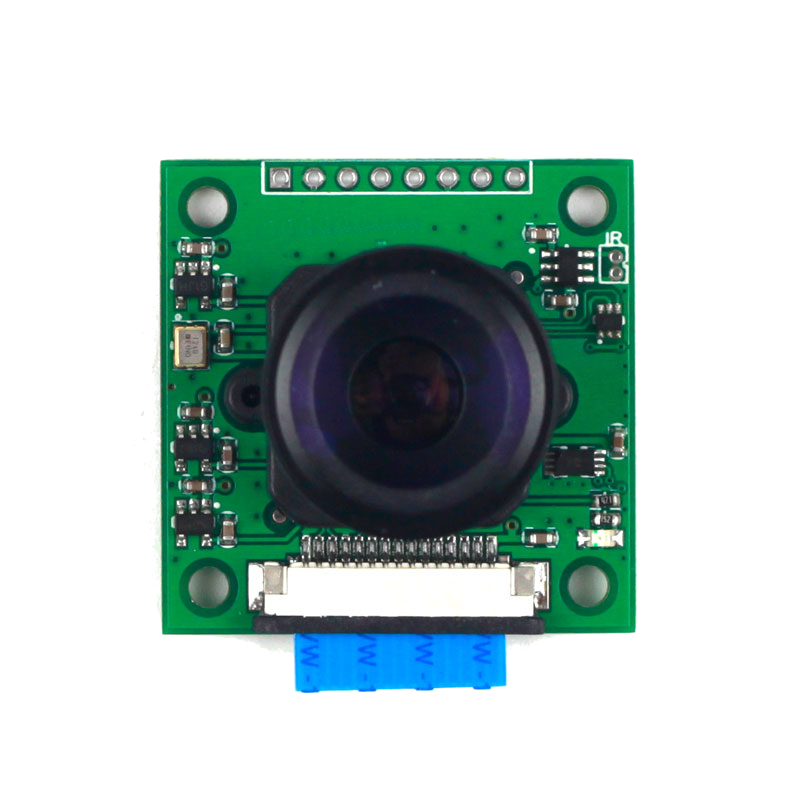
Latex/trabajo-de-investigacion-2/images/chapter5/tablas comparativas/camara simple 3.png
