pablodz/tesis_pregrado_pucp/Latex/trabajo-de-investigacion-2/images/chapter5/tablas comparativas/mecanismo de compuerta 2.png

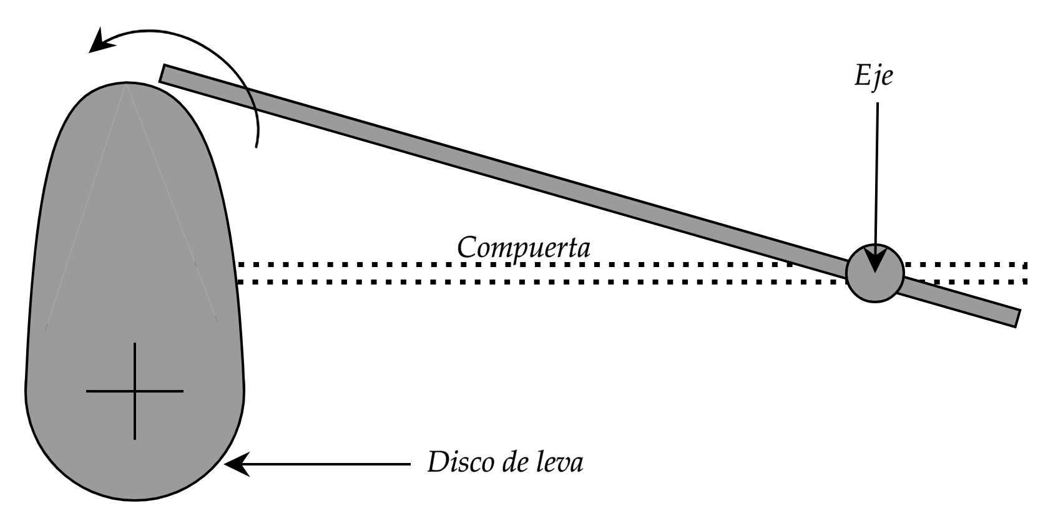
Latex/trabajo-de-investigacion-2/images/chapter5/tablas comparativas/mecanismo de compuerta 2.png
