pablodz/tesis_pregrado_pucp/Latex/trabajo-de-investigacion-2/images/chapter5/tablas comparativas/regulador de voltaje de conmutacion 1-1.png

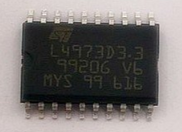
Latex/trabajo-de-investigacion-2/images/chapter5/tablas comparativas/regulador de voltaje de conmutacion 1-1.png
