pablodz/tesis_pregrado_pucp/Latex/trabajo-de-investigacion-2/images/chapter5/velocidad de compuerta.png

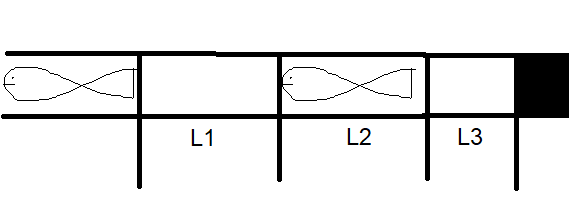
Latex/trabajo-de-investigacion-2/images/chapter5/velocidad de compuerta.png
