pablodz/tesis_pregrado_pucp/Latex/trabajo-de-investigacion-2/images/chapter5/ejemplo tabla plano ensamble.png

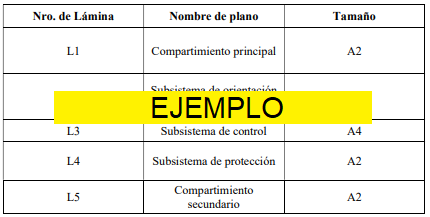
Latex/trabajo-de-investigacion-2/images/chapter5/ejemplo tabla plano ensamble.png
