pablodz/tesis_pregrado_pucp/Latex/trabajo-de-investigacion-2/images/chapter5/subensambles/control frontal.png

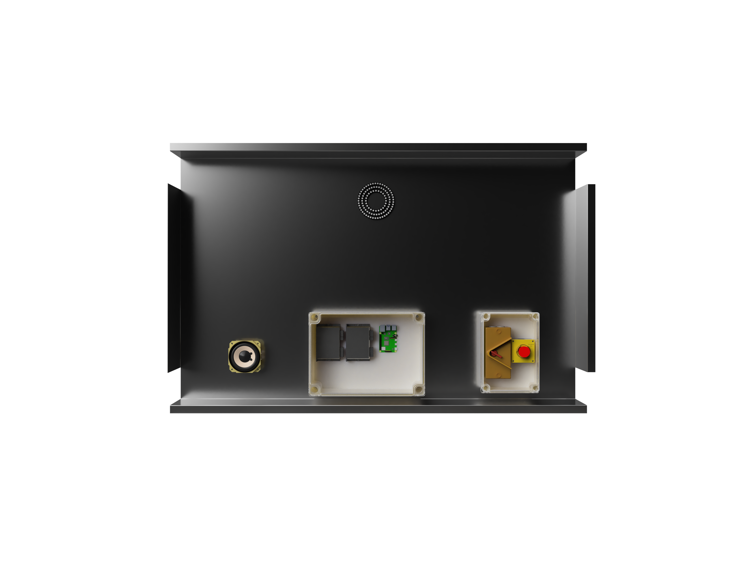
Latex/trabajo-de-investigacion-2/images/chapter5/subensambles/control frontal.png
