pablodz/tesis_pregrado_pucp/Latex/trabajo-de-investigacion-2/images/chapter5/subensambles/procesamiento de imagenes 2.png

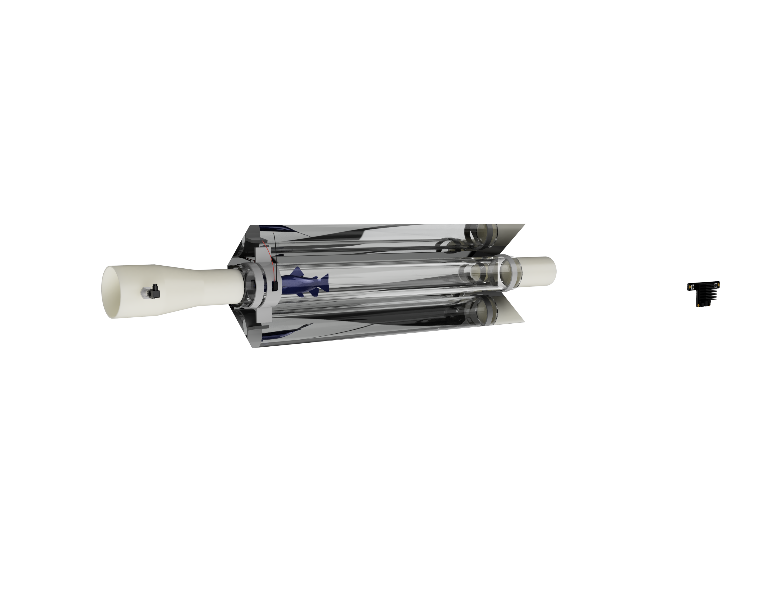
Latex/trabajo-de-investigacion-2/images/chapter5/subensambles/procesamiento de imagenes 2.png
