pablodz/tesis_pregrado_pucp/Latex/trabajo-de-investigacion-2/images/chapter5/subensambles/recepcion distribucion y traslado top.png

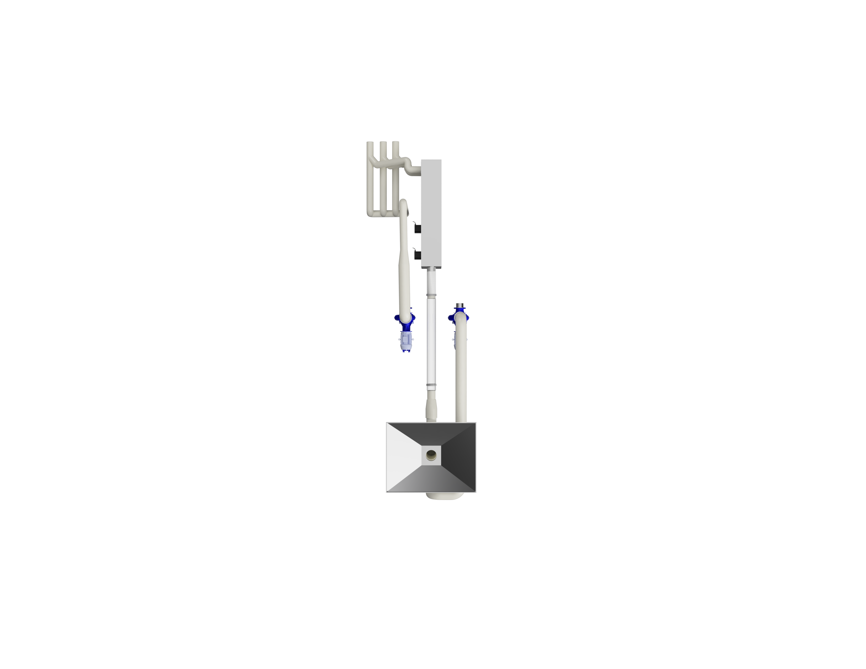
Latex/trabajo-de-investigacion-2/images/chapter5/subensambles/recepcion distribucion y traslado top.png
