pablodz/tesis_pregrado_pucp/Latex/trabajo-de-investigacion-2/images/chapter5/subensambles/sistema integral isometrico 1.png

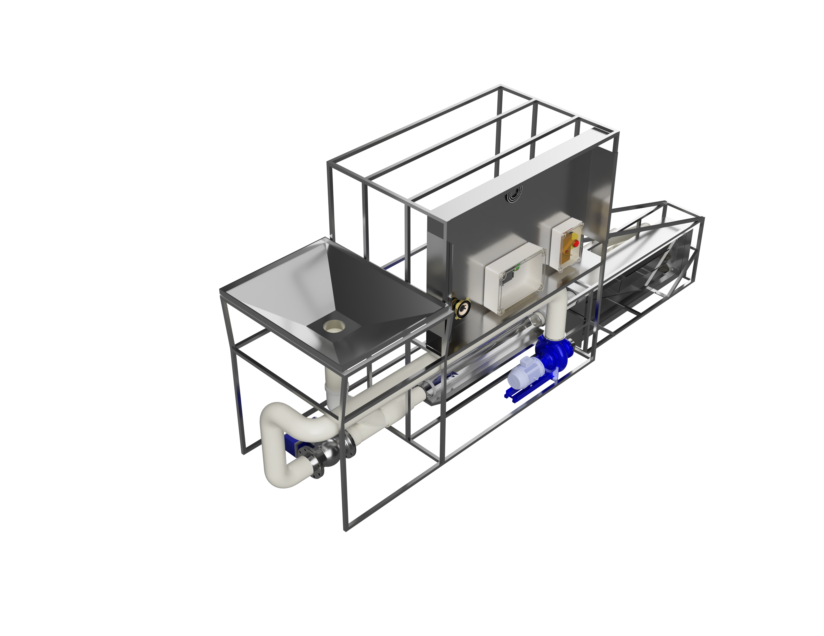
Latex/trabajo-de-investigacion-2/images/chapter5/subensambles/sistema integral isometrico 1.png
