pablodz/tesis_pregrado_pucp/Latex/trabajo-de-investigacion-2/images/chapter5/subensambles/subsistema de distribucion final.png

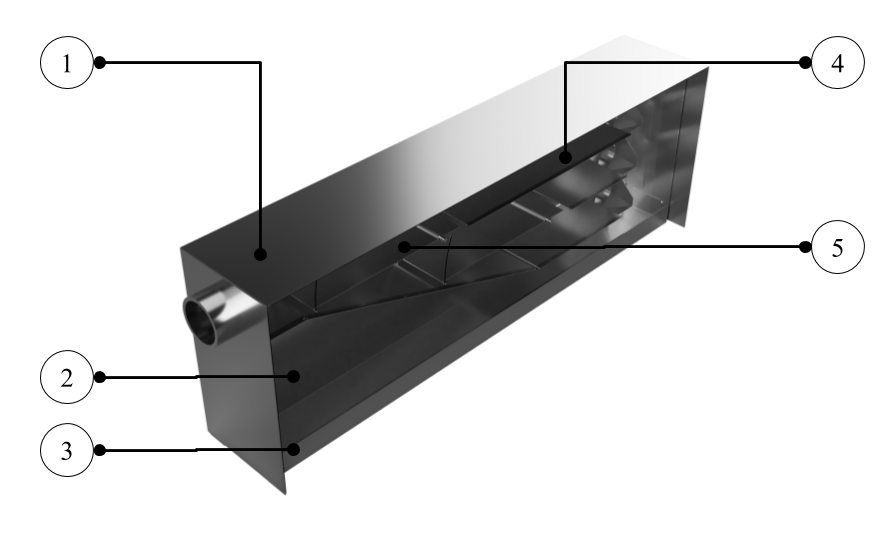
Latex/trabajo-de-investigacion-2/images/chapter5/subensambles/subsistema de distribucion final.png
